neilenns/CJ4-Autopilot/3D prints/Cap.stl

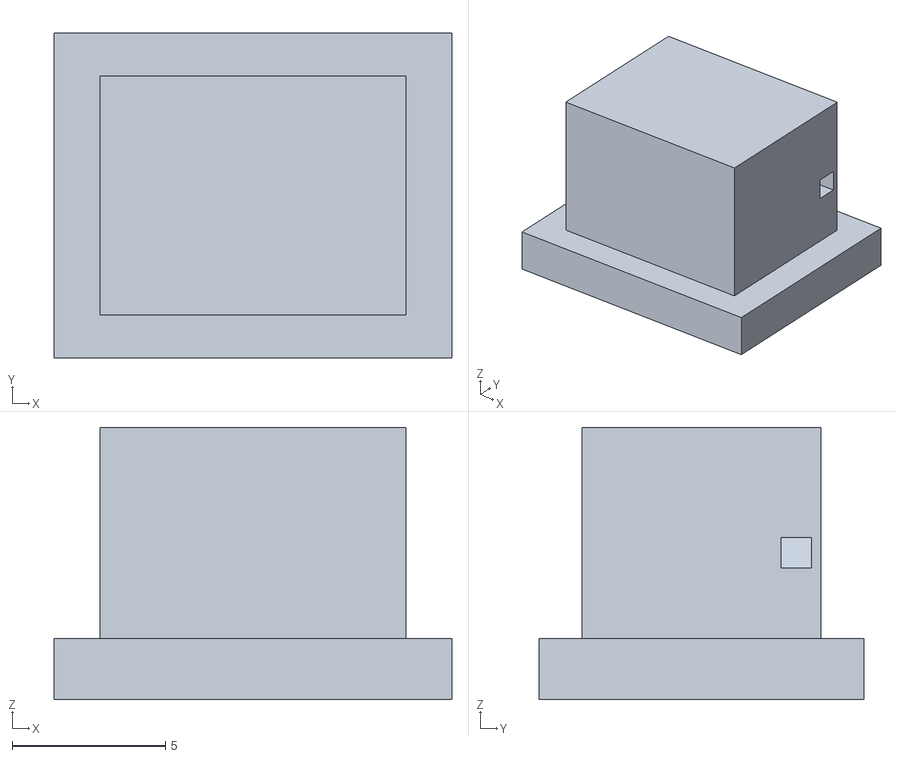
[picture p16: CAD file, 2022-10-01]
3D prints/Cap.stl
13.0 x 10.6 x 8.90
