neilenns/CJ4-Autopilot/3D prints/Mounting bracket - left.stl

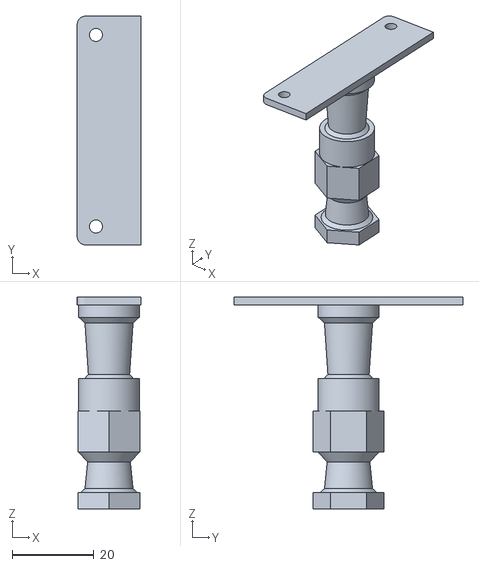
[picture p17: CAD file, 2022-10-01]
3D prints/Mounting bracket - left.stl
15.6 x 56.1 x 52.0
